luialvar/ultra_wideband_tumbler/old_uwb_reference_repo/embedded_uwb/rodos/tutorials/40-support-lib/matlib/rotations/00-referenzmanual.pdf

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

5 | Die Klasse AngleAxis
AngleAxis() | Erstellt das AngleAxis([0,0,0],0)
AngleAxis(const AngleAxis& other) | Copy-Konstruktor
AngleAxis(Vector3D& u,double phi) | Vektor-Winkel Konstruktor
AngleAxis(Quaternion& q) | Quaternion-Konstruktor
AngleAxis( Matrix3D& M) | Matrix-Konstruktor
AngleAxis(YPR& ypr) | AngleAxis Konstruktor
Quaternion toQuaternion() | AngleAxis zu Quaternion
Matrix3D toMatrix3D() | AngleAxis zu Matrix3D
YPR toYPR() | AngleAxis zu YPR
void print() | Konsolenausgabe
6 | Die Klasse Matrix4D
Matrix4D() | Erstellt die Identität
Matrix4D(Matrix3D& rot,Vector3D trans) | Matrix3D-Vector3D Konstruktor
Matrix4D(double* arr) | Array-Konstruktor
Matrix4D(const Matrix4D& other) | Copy-Konstruktor
Matrix3D getRotation() | Liefert Rotationsmatrix
Vector3D getTranslation() | Liefert Translation
Matrix4D scale(double factor) | homogene Matrixskalierung
Matrix4D mMult(const Matrix4D& right) | Matrixmultiplikation
Matrix4D invert() | inversion der Matrix4D
void print() | Konsolenausgabe
7 | Die Klasse CoordinateFrame3D
CoordinateFrame3D() | Erstellt ein Frame aus 4 Nullvektoren
CoordinateFrame3D(Vector3D& x, Vector3D& y,
Vector3D& z, Vector3D& origin) | 4 Vektor-Konstruktor
CoordinateFrame3D(Vector3D& x, Vector3D& y,
Vector3D& origin) | TRIAD-Konstruktor
CoordinateFrame3D(const CoordinateFrame3D& other) | Copy-Konstruktor
Matrix4D mapTo(CoordinateFrame3D& other) | Matrix4D von this nach other
CoordinateFrame3D translate(Vector3D& trans) | Verschiebt den Frame
CoordinateFrame3D rotate(Matrix3D& rot) | Rotiert den Frame mit einer Matrix
CoordinateFrame3D rotate(Quaternion& q) | Rotiert den Frame mit einem Quaternion
8 | Die Klasse TwoLineElement
TwoLineElement(string* twoLine) | Erstellt aus Stringarray ein TLE
9 | Die Klasse ComputationModel
ComputationModel(TwoLineElement tle) | TLE-Konstruktor
double* sgp4(double elapsedTime, TwoLineElement tle) | Berechnet Position nach SGP4

3

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
