luialvar/ultra_wideband_tumbler/old_uwb_reference_repo/embedded_uwb/rodos/tutorials/40-support-lib/matlib/rotations/00-praesentation.pdf

## Mathematische Bibliothek für Koordinatentransformationen und Rotationen

Markus Krug

2. Juli 2012
Markus Krug | Mathematische Bibliothek für Koordinatentransformationen und Rotationen

## Themen der Arbeit

Entwurf einer mathematischen Bibliothek für C++

## Themen der Arbeit

Entwurf einer mathematischen Bibliothek für C++ Quaternionen

## Themen der Arbeit

Entwurf einer mathematischen Bibliothek für C++ Quaternionen
Rotationsmatrizen

## Themen der Arbeit

Entwurf einer mathematischen Bibliothek für C++ Quaternionen
Rotationsmatrizen
homogene Koordinaten

## Themen der Arbeit

Entwurf einer mathematischen Bibliothek für C++ Quaternionen
Rotationsmatrizen
homogene Koordinaten
Koordinatentransformationen

## Themen der Arbeit

Entwurf einer mathematischen Bibliothek für C++ Quaternionen
Rotationsmatrizen
homogene Koordinaten
Koordinatentransformationen Fast-Fouriertransformation

## Themen der Arbeit

Entwurf einer mathematischen Bibliothek für C++ Quaternionen
Rotationsmatrizen
homogene Koordinaten
Koordinatentransformationen Fast-Fouriertransformation Kalmanlter

## Rotationen im R

2

0

y

x

v

φ

Vektor ~v mit φ = 45◦

## Rotationen im R

2

0

y

x

v

φ

0

Vektor ~v mit φ

0 = 60◦

## Rotationen im R

2

Was ist passiert?

## Rotationen im R

2

Was ist passiert?
eine Rotation von ~v um die z-Achse mit 15◦ (im Uhrzeigersinn)

## Rotationen im R

2

Was ist passiert?
eine Rotation von ~v um die z-Achse mit 15◦ (im Uhrzeigersinn)
eine Rotation des Koordinatensystems um −15◦ (gegen den
Uhrzeigersinn)

## Rotationen im R

2

Was ist passiert?
eine Rotation von ~v um die z-Achse mit 15◦ (im Uhrzeigersinn)
eine Rotation des Koordinatensystems um −15◦ (gegen den
Uhrzeigersinn)
eine Rotation von ~v um die z-Achse mit −345◦ (gegen den
Uhrezeigersinn)

## Rotationen im R

2

Was ist passiert?
eine Rotation von ~v um die z-Achse mit 15◦ (im Uhrzeigersinn)
eine Rotation des Koordinatensystems um −15◦ (gegen den
Uhrzeigersinn)
eine Rotation von ~v um die z-Achse mit −345◦ (gegen den
Uhrezeigersinn)
eine Rotation des Koordinatensystems um 345◦ (im
Uhrzeigersinn)

## Rotationen im R

2

Was ist passiert?
eine Rotation von ~v um die z-Achse mit 15◦ (im Uhrzeigersinn)
eine Rotation des Koordinatensystems um −15◦ (gegen den
Uhrzeigersinn)
eine Rotation von ~v um die z-Achse mit −345◦ (gegen den
Uhrezeigersinn)
eine Rotation des Koordinatensystems um 345◦
(im
Uhrzeigersinn)
⇒ es muss immer dazugesagt werden wovon man gerade Redet sonst stets Unklar !

## Möglichkeiten eine Rotation zu beschreiben

Welche Möglichkeiten gibt es eine Rotation zu beschreiben ?

## Möglichkeiten eine Rotation zu beschreiben

Welche Möglichkeiten gibt es eine Rotation zu beschreiben ? 1 Rotationsmatrizen

## Möglichkeiten eine Rotation zu beschreiben

Welche Möglichkeiten gibt es eine Rotation zu beschreiben ?
1 | Rotationsmatrizen
2 | Achse und Winkel

## Möglichkeiten eine Rotation zu beschreiben

Welche Möglichkeiten gibt es eine Rotation zu beschreiben ?
1 | Rotationsmatrizen
2 | Achse und Winkel
3 | Eulerwinkel(in der Luftfahrt Yaw,Pitch und Roll)

## Möglichkeiten eine Rotation zu beschreiben

Welche Möglichkeiten gibt es eine Rotation zu beschreiben ?
1 | Rotationsmatrizen
2 | Achse und Winkel
3 | Eulerwinkel(in der Luftfahrt Yaw,Pitch und Roll)
4 | Quaternionen

## Beschreibung durch eine Rotationsmatrix

Zurück zum Beispiel: 0

y

x

v

φ
x1

y1

x1 = cos φ · |~v|
y1 = sin φ · |~v|

## Beschreibung durch eine Rotationsmatrix

Analog gilt: 0

y

x

v

φ

0
x2

y2

x2 = cos φ

0
- |~v|
y2 = sin φ

0
- |~v|

## Additionstheoreme, jeder kennt sie keiner kann sie

mit φ

0 = φ + α folgt:

x2 =

cos φ cos α−sin φ sin α
z | }| | {
cos(φ + α) | ·|~v|
y2 = | sin(φ + α)
| | {z | }
sin φ cos α+sin α cos φ

·|~v|

x2 = cos φ · |~v|
| {z | }
x1 | | cos α − sin φ · |~v|
| {z | }
y1

cos α

y2 = sin φ · |~v|
| {z }
y1

cos α + cos φ · |~v|
| {z }
x1

sin α

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

## Ausdehnung auf den R

3

Da die Rotation ausschlieÿlich in der xy-Ebene stattndet, so wird die z-Komponente des Vektors ~v nicht verändert
⇒ es wurde die Fundamentalmatrix um die z-Achse gefunden:

Rz (α) =

cos α − sin α 0
sin α | cos α | 0
0 | 0 | 1

## Fundamentalrotationen

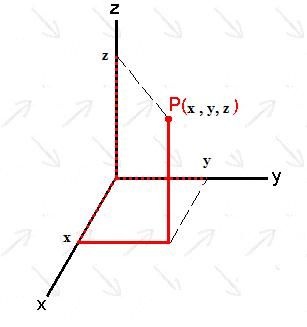
[picture p46: figure]

Abbildung : Die Projektion in die xy-Ebene

## Fundamentalrotationen

Betrachtet man nun Projektionen in die xz bzw. yz-Ebene, so erhält man die Fundamentalrotationsmatrizen:

Rz (α) =

cos α − sin α 0
sin α | cos α | 0
0 | 0 | 1

Ry (β) =

cos β | 0 sin β
0 | 1 | 0
− sin β 0 cos β

Rx (γ) =

1 | 0 | 0
0 cos γ − sin γ
0 sin γ cos γ

## Fundamentalrotationen

# Was bringt uns das nun ?

## Fundamentalrotationen

Was bringt uns das nun ?

W
ir können mit Hilfe einer einfachen Rechenvorschrift eine Rotation eines Vektors ~v mit einen Winkel φ um eine der Koordinatenachsen vollziehen

w~ = R(φ) · ~v

## Fundamentalrotationen

# Was können wir noch nicht ?

## Fundamentalrotationen

Was können wir noch nicht ?
⇒ eine Rotation um einen beliebigen Vektor

## Fundamentalrotationen

Was können wir noch nicht ?
⇒ eine Rotation um einen beliebigen Vektor Abhilfe schat das Theorem von Euler:

Satz (Eulers Theorem)
Zwei voneinander unabhängige, orthonormale Koordinatensysteme können durch eine Folge von nicht mehr als 3 Fundamentalrotationen, wobei keine zwei aufeinanderfolgenden Rotationen um die selbe Achse erfolgen, ineinander überführt werden.

## Eulerwinkel

Es ergeben sich folgende 12 Möglichkeiten das Eulertheorem anzuwenden:
xyz yzx zxy
xzy yxz zyx
xyx yzy zxz
xzx yxy zyz

## Eulerwinkel

Es ergeben sich folgende 12 Möglichkeiten das Eulertheorem anzuwenden:
xyz yzx zxy
xzy yxz zyx
xyx yzy zxz
xzx yxy zyz
zyx bedeutet beispielsweise:

1 eine Rotation um die z-Achse

## Eulerwinkel

Es ergeben sich folgende 12 Möglichkeiten das Eulertheorem anzuwenden:
xyz yzx zxy
xzy yxz zyx
xyx yzy zxz
xzx yxy zyz
zyx bedeutet beispielsweise:
1 | eine Rotation um die z-Achse
2 | eine Rotation um die neue y-Achse

## Eulerwinkel

Es ergeben sich folgende 12 Möglichkeiten das Eulertheorem anzuwenden:
xyz yzx zxy
xzy yxz zyx
xyx yzy zxz
xzx yxy zyz
zyx bedeutet beispielsweise:
1 | eine Rotation um die z-Achse
2 | eine Rotation um die neue y-Achse
3 | eine Rotation um die neue x-Achse

## Eulerwinkel

Es ergeben sich folgende 12 Möglichkeiten das Eulertheorem anzuwenden:
xyz yzx zxy
xzy yxz zyx
xyx yzy zxz
xzx yxy zyz
zyx bedeutet beispielsweise:
1 | eine Rotation um die z-Achse
2 | eine Rotation um die neue y-Achse
3 | eine Rotation um die neue x-Achse

⇒ Yaw-Pitch-Roll Luftfahrtsequenz

## Rotationssequenzen

Das Schlüsselwort neue:
Es ergeben sich 2 Möglichkeiten die Eulersequenz nachzurechnen:

Multiplikation von rechts

## Rotationssequenzen

Das Schlüsselwort neue:
Es ergeben sich 2 Möglichkeiten die Eulersequenz nachzurechnen:

Multiplikation von rechts
Multiplikation von links

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

## Rotationssequenzen

Goldene Merkregel für Rotationssequenzen:

Faustregel (Rotationssequenzen)
Erfolgt eine Rotation um eine der xen Achsen, so ist stets von links zu Multiplizieren, eine Rotation um eine der neuen Achsen wird stets von rechts Multipliziert.

## Eulerwinkel

Für die zuvor vorgestellte Eulersequenz zyx gilt also:

Rzyx (α, β, γ) = Rz (α) · Ry (β) · Rx (γ)

Die Winkel α, β, γ werden als Eulerwinkel bezeichnet

## Yaw-Pitch-Roll Matrix

Für die zuvor vorgestellte Eulersequenz zyx gilt also:

Rzyx (α, β, γ) = Rz (α) · Ry (β) · Rx (γ)

=

cos α cos β cos α sin β sin γ − sin α cos γ cos α sin β cos γ + sin α sin γ
sin α cos β | sin α sin β sin γ + cos α cos γ sin α sin β cos γ − cos α sin γ
− sin β | cos β sin γ | cos β cos γ

!

## YPR Matrix

Was haben wir gelernt:
Mit Hilfe der YPR-Matrix können wir also einen Vektor mit den Eulerwinkeln drehen.

## YPR Matrix

Was haben wir gelernt:
Mit Hilfe der YPR-Matrix können wir also einen Vektor mit den Eulerwinkeln drehen.
Wir sind nicht mehr eingeschränkt auf reine Rotationen um die Koordinatensystemachsen.

## YPR Matrix

Was haben wir gelernt:
Mit Hilfe der YPR-Matrix können wir also einen Vektor mit den Eulerwinkeln drehen.
Wir sind nicht mehr eingeschränkt auf reine Rotationen um die Koordinatensystemachsen.
Was wir jedoch immer noch nicht können ist eine Rotation um einen beliebigen Vektor und Winkel

## allgemeine Rotationsmatrix

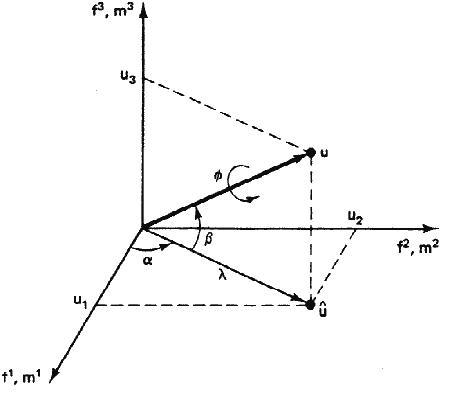
[picture p47: figure]

Abbildung : Eine Rotation um einen beliebigen Vektor ~u mit Winkel φ

## allgemeine Rotationsmatrix

Zur Herleitung der allgemeinen Matrix müssen folgende Schritte ausgeführt werden:

## allgemeine Rotationsmatrix

Zur Herleitung der allgemeinen Matrix müssen folgende Schritte ausgeführt werden:
1 Drehe M um m³ mit dem Winkel α

## allgemeine Rotationsmatrix

Zur Herleitung der allgemeinen Matrix müssen folgende Schritte ausgeführt werden:
1 | Drehe M um m³ mit dem Winkel α
2 | Drehe M um m² mit dem Winkel −β

## allgemeine Rotationsmatrix

Zur Herleitung der allgemeinen Matrix müssen folgende Schritte ausgeführt werden:
1 | Drehe M um m³ mit dem Winkel α
2 | Drehe M um m² mit dem Winkel −β
3 | Drehe M um m¹ mit dem Winkel φ

## allgemeine Rotationsmatrix

Zur Herleitung der allgemeinen Matrix müssen folgende Schritte ausgeführt werden:
1 | Drehe M um m³ mit dem Winkel α
2 | Drehe M um m² mit dem Winkel −β
3 | Drehe M um m¹ mit dem Winkel φ
4 | Drehe M um m² mit dem Winkel β

## allgemeine Rotationsmatrix

Zur Herleitung der allgemeinen Matrix müssen folgende Schritte ausgeführt werden:
1 | Drehe M um m³ mit dem Winkel α
2 | Drehe M um m² mit dem Winkel −β
3 | Drehe M um m¹ mit dem Winkel φ
4 | Drehe M um m² mit dem Winkel β
5 | Drehe M um m³ mit dem Winkel −α

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

## kleine Ergebniszusammenfassung

Wir können nun:
Rotationen um die Koordinatenachsen
Rotationen mit Hilfe von Eulerwinkeln
Rotationen um einen beliebigen Vektor mit einem beliebigen Winkel

## kleine Ergebniszusammenfassung

Wir können nun:
Rotationen um die Koordinatenachsen
Rotationen mit Hilfe von Eulerwinkeln
Rotationen um einen beliebigen Vektor mit einem beliebigen Winkel
Doch alles hat noch einen Nachteil:
⇒ wir müssen stets zuerst die Rotationsmatrix bilden und damit die Rotation ausführen

w~ = R · ~v

## Rodrigues Rotationsformel

Betrachtet man die allgemeine Rotation eines Vektors ~v =

v1
v2
v3

mit der allgemeinen Rotationsmatrix:

w~ =

u

2

x

(1 − cos φ) + cos φ | ux uy (1 − cos φ) − uz sin φ | ux uz (1 − cos φ) + uy sin φ
ux uy (1 − cos φ) + uz sin φ | u
| 2 y
| (1 − cos φ) + cos φ | uy uz (1 − cos φ) − ux sin φ
ux uz (1 − cos φ) − uy sin φ | uy uz (1 − cos φ) + ux sin φ | u
| | 2 z (1 − cos φ) + cos φ
- ~v

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

## Rodrigues Rotationsformel

Cleveres zusammenfassen ergibt die Rodrigues Rotationsformel:

vRot ~ = ~v cos φ + (~u × ~v)sin φ + ~u(~u · ~v)(1 − cos φ)

## Rodrigues Rotationsformel

Cleveres zusammenfassen ergibt die Rodrigues Rotationsformel:

vRot ~ = ~v cos φ + (~u × ~v)sin φ + ~u(~u · ~v)(1 − cos φ)

⇒ es ist also auch möglich einen Vektor um einen gegebenen Vektor (und Winkel) zu rotieren ohne zunächst die allgemeine Rotationsmatrix bilden zu müssen.

## Vor- und Nachteile der bisherigen Darstellungen

Vorteile der Eulerwinkel:
nur 3 Variablen müssen gespeichert werden
am einfachsten aus den Sensordaten zu gewinnen (Strapdown-Algorithmus)

## Vor- und Nachteile der bisherigen Darstellungen

Nachteile der Eulerwinkel:
es muss jedesmal zunächst die Rotationsmatrix gebildet werden Gimbal Locks

## Vor- und Nachteile der bisherigen Darstellungen

Vorteile der Achse-Winkel Darstellung
es kann ohne die Rotationsmatrix bilden zu müssen rotiert werden
Skaliert man den Winkel in die Länge des Vektors nur 3 Variablen zu speichern

## Vor- und Nachteile der bisherigen Darstellungen

Nachteile der Achse-Winkel Darstellung
es können keine Rotationssequenzen berechnet werden (immer einzeln !)

## Vor- und Nachteile der bisherigen Darstellungen

Vorteile der Rotationsmatrizen allgemein relativ anschaulich

## Vor- und Nachteile der bisherigen Darstellungen

Nachteile der Rotationsmatrizen sehr Rechenaufwändig
sehr Speicheraufwändig

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

## Quaternionen

Quaternionen H als Hyperkomplexe Zahlen des Ranges 4

Angefangen bei R

Verdopplungssatz
z}|{ ⇒ | C

von den komplexen Zahlen C

Verdopplungssatz
z}|{ ⇒ | H

Quaternion ist also ein 4-Tupel
(q0, q1, q2, q3) = q0 + iq1 + jq2 + kq3

## Quaternionen

i, j, k interpretiert man als Einheitsvektoren im 3-dimensionalen Raum.
Die Quaternionen enthalten also den R

3
als Spezialfall für q0 = 0 Ein 3-dimensionaler Vektor ~v kann mit Hilfe der Quaternionen also dargestellt werden,als:

~v = 0 + ~v = q0 + ~q

## Quaternionen-Rechenregeln

Analog zum R

4 deniert man die Gleichheit zweier Quaternionen p und q, als:
q0 = p0 | q1 = p1 | q2 = p2 | q3 = p3

## Quaternionen-Rechenregeln

Analog zum R

4 deniert man die Gleichheit zweier Quaternionen p und q, als:
q0 = p0 | q1 = p1 | q2 = p2 | q3 = p3
und deren Addition:

p + q = (p0 + q0) + i(p1 + q1) + j(p2 + q2) + k(p3 + q3)

## Quaternionen-Multiplikation

Multipliziert man nach altbekannten Rechenregeln zwei Quaternion p und q, so erhält man :

pq = (p0 + p1 + p2 + p3)(q0 + q1 + q2 + q3)

## Quaternionen-Multiplikation

Multipliziert man nach altbekannten Rechenregeln zwei Quaternion p und q, so erhält man :

pq = (p0 + p1 + p2 + p3)(q0 + q1 + q2 + q3) = p0q0 + ip0q1 + jp0q2 + kp0q3

+ ip1q0 + i

2
p1q1 + ijp1q2 + ikp1q3

+ jp2q0 + jip2q1 + j

2
p2q2 + jkp2q3

+ kp3q0 + kip3q1 + kjp3q2 + k

2
p3q3

## Quaternionen-Multiplikation

Um daraus ein nützliches Ergebnis ziehen zu können benötigen wir die Rechenregeln von Hamilton

i

2 = j

2 = k

2 = ijk = −1

ij = k = −ji
jk = i = −kj
ki = j = −ik

## Quaternionen-Multiplikation

Um daraus ein nützliches Ergebnis ziehen zu können benötigen wir die Rechenregeln von Hamilton

i

2 = j

2 = k

2 = ijk = −1

ij = k = −ji
jk = i = −kj
ki = j = −ik

mit deren Hilfe dann gilt:

pq = p0q0 − (p1q1 + p2q2 + p3q3)
+ p0(iq1 + jq2 + kq3) + q0(ip1 + jp2 + kp3)
+ i(p2q3 − p3q2) + j(p3q1 − p1q3) + k(p1q2 − p2q1)

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

## Quaternionen-Multiplikation

pq = p0q0 −

~p·~q
z | }| | {
(p1q1 + p2q2 + p3q3)

+

p0·~q
z | }| | {
p0(iq1 + jq2 + kq3) +q0(ip1 + jp2 + kp3)
+ i(p2q3 − p3q2) + j(p3q1 − p1q3) + k(p1q2 − p2q1)

## Quaternionen-Multiplikation

pq = p0q0 −

~p·~q
z | }| | {
(p1q1 + p2q2 + p3q3)

+

p0·~q
z | }| | {
p0(iq1 + jq2 + kq3) +

q0·~p
z | }| | {
q0(ip1 + jp2 + kp3)
+ i(p2q3 − p3q2) + j(p3q1 − p1q3) + k(p1q2 − p2q1)

## Quaternionen-Multiplikation

pq = p0q0 −

~p·~q
z | }| | {
(p1q1 + p2q2 + p3q3)

+

p0·~q
z | }| | {
p0(iq1 + jq2 + kq3) +

q0·~p
z | }| | {
q0(ip1 + jp2 + kp3)
+ i(p2q3 − p3q2) + j(p3q1 − p1q3) + k(p1q2 − p2q1)
| | {z | }
~p×~q

## Quaternionen-Multiplikation

Damit wurde die wohl am leichtesten per Hand zu berechnende Variante gefunden:

pq = p0q0 − ~p · ~q + p0~q + q0~p + ~p × ~q

oder analog in Matrixschreibweise:

pq = r =

r0
r1
r2
r3

=

p0 | −p1 | −p2 | −p3
p1 | p0 | −p3 | p2
p2 | p3 | p0 | −p1
p3 | −p2 | p1 | p0

q0
q1
q2
q3

## konjugiertes Quaternionen

Zum Beschreiben, warum ein Quaternion eine Rotation darstellt, wird noch eine letzte Rechenregel für Quaternionen benötigt, ähnlich wie bei den komplexen Zahlen C deniert man sich das konjugierte Quaternion als:

q

∗ = q0 − (iq1 + jq2 + kq3)

## Das Quaternion als Rotation

Zurück zu Rotationsmatrizen, wir wissen:

w~ = R · ~v

beschreibt eine Rotation mit einer Matrix. Gesucht ist nun ein ähnlicher Audruck für ein Quaternion.

## Das Quaternion als Rotation

Zurück zu Rotationsmatrizen, wir wissen:

w~ = R · ~v

beschreibt eine Rotation mit einer Matrix. Gesucht ist nun ein ähnlicher Audruck für ein Quaternion. Instinktiv versucht man zunächst:

w~ = q · ~v

Berechnet man nun das obige Quaternionenprodukt, so ergibt sich:

w~ = q · ~v = (q0 + ~q)(0 + ~v)
= q0 · 0 − ~q · ~v + 0 · ~q + q0~v + ~q × ~v = −~q · ~v + q0~v + ~q × ~v

## Das Quaternion als Rotation

Zurück zu Rotationsmatrizen, wir wissen:

w~ = R · ~v

beschreibt eine Rotation mit einer Matrix. Gesucht ist nun ein ähnlicher Audruck für ein Quaternion. Instinktiv versucht man zunächst:

w~ = q · ~v

Berechnet man nun das obige Quaternionenprodukt, so ergibt sich:

w~ = q · ~v = (q0 + ~q)(0 + ~v)
= q0 · 0 − ~q · ~v + 0 · ~q + q0~v + ~q × ~v = −~q · ~v + q0~v + ~q × ~v

Wir liegen nur in R

3
, wenn q0 = 0 und damit:

~q · ~v = 0

## Das Quaternion als Rotation

Wir liegen also nur in R

3
, wenn ~q senkrecht auf ~v steht: ⇒erster Ansatz im allgemeinen nicht aufrecht zu erhalten ! Zweiter Ansatz:
vpq , vqp , pqv
qpv , pvq , qvp

## Das Quaternion als Rotation

Wir liegen also nur in R

3
, wenn ~q senkrecht auf ~v steht: ⇒erster Ansatz im allgemeinen nicht aufrecht zu erhalten ! Zweiter Ansatz:
vpq , vqp , pqv
qpv , pvq , qvp
Das Produkt pq ist wieder ein Quaternion also bleibt nur pvq und qvp.

## Das Quaternion als Rotation

Berechnet man das Produkt p~v q, so ergibt sich für den skalaren Anteil w0:

w0 = −q0(~p · ~v) − p0(~v · ~q) + (~p × ~q) · ~v

## Das Quaternion als Rotation

Berechnet man das Produkt p~v q, so ergibt sich für den skalaren Anteil w0:

w0 = −q0(~p · ~v) − p0(~v · ~q) + (~p × ~q) · ~v

Setzt man nun noch q = p

∗
ein, so folgt:

w0 = −p0(~p · ~v) − p0(~v · −~p) + (~p × −~p) · ~v = −p0[~p · ~v + (−~v · ~p)] + 0

= 0

## Das Quaternion als Rotation

Berechnet man das Produkt p~v q, so ergibt sich für den skalaren Anteil w0:

w0 = −q0(~p · ~v) − p0(~v · ~q) + (~p × ~q) · ~v

Setzt man nun noch q = p

∗
ein, so folgt:

w0 = −p0(~p · ~v) − p0(~v · −~p) + (~p × −~p) · ~v = −p0[~p · ~v + (−~v · ~p)] + 0

= 0

Ab jetzt wird der Term q~v q∗ als Quaternionenrotationsoperator Lv (q) bezeichnet.

## Quaternionen-Der Achse-Winkel Charakter

Wir wissen q = q0 + ~q.
Für ein normiertes Quaternion gilt:

q

2
0 + |~q|

2 = 1

## Quaternionen-Der Achse-Winkel Charakter

Wir wissen q = q0 + ~q.
Für ein normiertes Quaternion gilt:

q

2
0 + |~q|

2 = 1

Erinnerung: Pythagoras am Einheitskreis!

cos² φ + sin² φ = 1

## Quaternionen-Der Achse-Winkel Charakter

Wir wissen q = q0 + ~q.
Für ein normiertes Quaternion gilt:

q

2
0 + |~q|

2 = 1

Erinnerung: Pythagoras am Einheitskreis!

cos² φ + sin² φ = 1

Daraus folgern wir:

cos² φ = q

2
0
sin² φ = |~q|

2

## Quaternionen-Der Achse-Winkel Charakter

Wir wissen q = q0 + ~q.
Für ein normiertes Quaternion gilt:

q

2
0 + |~q|

2 = 1

Erinnerung: Pythagoras am Einheitskreis!

cos² φ + sin² φ = 1

Daraus folgern wir:

cos² φ = q

2
0
sin² φ = |~q|

2

Man kann also allgemein für ein Quaternion schreiben:

q = q0 + ~q = cos φ + ~u sin φ

## Quaternionen-Der Achse-Winkel Charakter

q = q0 + ~q = cos φ + ~u sin φ

## Quaternionen-Der Achse-Winkel Charakter

q = q0 + ~q = cos φ + ~u sin φ

~u wird sich noch als Rotationsachse herausstellen

## Quaternionen-Der Achse-Winkel Charakter

q = q0 + ~q = cos φ + ~u sin φ

~u wird sich noch als Rotationsachse herausstellen φ scheint in jedem Fall im Zusammenhang mit dem Rotationswinkel zu stehen

## Quaternionen-Der Achse-Winkel Charakter

q = q0 + ~q = cos φ + ~u sin φ

~u wird sich noch als Rotationsachse herausstellen
φ scheint in jedem Fall im Zusammenhang mit dem Rotationswinkel zu stehen
⇒ der Achse-Winkel Charackter des Quaternions wird deutlich!

## Quaternionen-Der Achse-Winkel Charakter

q = q0 + ~q = cos φ + ~u sin φ

~u wird sich noch als Rotationsachse herausstellen
φ scheint in jedem Fall im Zusammenhang mit dem Rotationswinkel zu stehen
⇒ der Achse-Winkel Charackter des Quaternions wird deutlich! es wird nun Zeit zu zeigen, dass das Quaternion auch eine Rotation darstellt!

## Quaternionen-Der Achse-Winkel Charakter

q = q0 + ~q = cos φ + ~u sin φ

~u wird sich noch als Rotationsachse herausstellen
φ scheint in jedem Fall im Zusammenhang mit dem Rotationswinkel zu stehen
⇒ der Achse-Winkel Charackter des Quaternions wird deutlich! es wird nun Zeit zu zeigen, dass das Quaternion auch eine Rotation darstellt!
Ab jetzt im Hinterkopf behalten, wir behandeln normierte Quaternionen

## Der Quaternionrotationsoperator Lq(v)

Wir benötigen noch eine Kurzschreibweise:

Lq(v) = q~v q∗

Und das fertig vereinfachte Ergebnis der Multiplikation:

w~ = qvq∗ = (q0 + ~q)(0 + ~v)(q0 − ~q)

## Der Quaternionrotationsoperator Lq(v)

Wir benötigen noch eine Kurzschreibweise:

Lq(v) = q~v q∗

Und das fertig vereinfachte Ergebnis der Multiplikation:

w~ = qvq∗ = (q0 + ~q)(0 + ~v)(q0 − ~q)

= (2q

2
0 − 1)~v + 2(~q · ~v)~q + 2q0(~q × ~v)

## Der Quaternionrotationsoperator Lq(v)

Wir benötigen noch eine Kurzschreibweise:

Lq(v) = q~v q∗

Und das fertig vereinfachte Ergebnis der Multiplikation:

w~ = qvq∗ = (q0 + ~q)(0 + ~v)(q0 − ~q)

= (2q

2
0 − 1)~v + 2(~q · ~v)~q + 2q0(~q × ~v)

= (q

2
0 − |~q|

2
)~v + 2(~q · ~v)~q + 2q0(~q × ~v)

## Der Quaternionrotationsoperator Lq(v)

Wir benötigen noch eine Kurzschreibweise:

Lq(v) = q~v q∗

Und das fertig vereinfachte Ergebnis der Multiplikation:

w~ = qvq∗ = (q0 + ~q)(0 + ~v)(q0 − ~q)

= (2q

2
0 − 1)~v + 2(~q · ~v)~q + 2q0(~q × ~v)

= (q

2
0 − |~q|

2
)~v + 2(~q · ~v)~q + 2q0(~q × ~v)

Sowie 2 Eigenschaften des Operators:
1 | Linearität I : Lq(a + b) = Lq(a) + Lq(b)
2 | Linearität II: Lq(ka) = k · Lq(a)

## Beweis- Lq(v) beschreibt eine Rotation

Trick: zerlege den zu rotierenden Vektor ~v in 2 Teile:

~v =

parallel zu ~q
z}|{
~a +

senkrecht zu ~q
z}|{
~n = k~q + ~n
w~ = ~b + m~

## Beweis- Lq(v) beschreibt eine Rotation

Trick: zerlege den zu rotierenden Vektor ~v in 2 Teile:

~v =

parallel zu ~q
z}|{
~a +

senkrecht zu ~q
z}|{
~n = k~q + ~n
w~ = ~b + m~

Was uns schon klar sein sollte, der zur Rotationsachse parallel Anteil bleibt bei der Rotation unverändert!

## Der parallele Anteil a

Wegen der Linearität von Lq(v) gilt:

w~ = Lq(v) = Lq(a + n) = Lq(a) + Lq(n)

Was uns erlaubt beide Teile separat zu betrachten.

## Der parallele Anteil a

Wegen der Linearität von Lq(v) gilt:

w~ = Lq(v) = Lq(a + n) = Lq(a) + Lq(n)

Was uns erlaubt beide Teile separat zu betrachten.

Lq(a) = Lq(k · ~q) Wobei k ein Skalar darstellt = q(k~q)q

∗

= (q

2
0 − |~q|

2
)(k~q) + 2(~q · k~q)~q + 2q0(~q × k~q) = kq²
0

~q − k|~q|

2
~q + 2k|~q|

2
~q

= k(q

2
0 + |~q|

2
)
= k~q = a

## Der senkrechte Anteil

Lq(n) = (q

2
0 − |~q|

2
)n + 2q0|~q|(~u × ~n)
= n(cos² φ − sin² φ) + 2 cos φ sin φ(~u × ~n)

= n cos(2φ) + (~u × ~n)sin(2φ)

Vermutung: Rotation um die Achse ~u mit dem Winkel 2φ

## Vermutung bestätigen!

Lq(n) = n cos(2φ) + (~u × ~n)sin(2φ)

Wir haben bereits gelernt wie man einen Vektor ~v um einen gegebenen Vektor und einen gegebenen Winkel rotiert.

## Vermutung bestätigen!

Lq(n) = n cos(2φ) + (~u × ~n)sin(2φ)

Wir haben bereits gelernt wie man einen Vektor ~v um einen gegebenen Vektor und einen gegebenen Winkel rotiert. ⇒ Rodrigues Rotationsformel.

## Vermutung bestätigen!

Lq(n) = n cos(2φ) + (~u × ~n)sin(2φ)

Wir haben bereits gelernt wie man einen Vektor ~v um einen gegebenen Vektor und einen gegebenen Winkel rotiert. ⇒ Rodrigues Rotationsformel.

nRot = n cos(2φ) + (~u × ~n)sin(2φ) + ~u(~u · ~n)(1 − cos(2φ) = n · cos(2φ) + (~u × ~n)sin(2φ)

## Wichtige Schlussfolgerung

Für jedes Einheitsquaternion q = q0 + ~q = cosφ + ~u sin φ und für jeden Vektor ~v ∈ R

3
, beschreibt der Quaternionrotationsoperator Lq(v) = q~v q∗
eine Rotation von ~v um die Achse ~u =

~q
|~q| mit dem
Winkel 2φ.

## Wichtige Schlussfolgerung

Für jedes Einheitsquaternion q = q0 + ~q = cosφ + ~u sin φ und für jeden Vektor ~v ∈ R

3
, beschreibt der Quaternionrotationsoperator Lq(v) = q~v q∗
eine Rotation von ~v um die Achse ~u =

~q
|~q| mit dem
Winkel 2φ.

Analog soll im Folgenden der Operator Lq
∗ = q

∗~v q deniert sein
als:

Für jedes Einheitsquaternion q = q0 + ~q = cosφ + ~u sin φ und für jeden Vektor ~v ∈ R

3
, beschreibt der Quaternionrotationsoperator Lq

∗ = q

∗~v q eine Rotation von ~v um die Achse ~u =

~q
|~q| mit dem
Winkel −2φ.

## Arten der Rotation

Es wurde nun festgestellt, dass eine Rotation über die Folgenden 2 Gleichungen ausgeführt werden kann:

w~ = R · ~v
w~ = q~v q∗

## Arten der Rotation

Es wurde nun festgestellt, dass eine Rotation über die Folgenden 2 Gleichungen ausgeführt werden kann:

w~ = R · ~v
w~ = q~v q∗

Damit kann der Zusammenhang zwischen Quaternion und Rotationsmatrix ermittelt werden:

R · ~v = q~v q∗

## Zusammenhang zwischen Quaternionen und Rotationsmatrix

es ist bereits bekannt, dass:

w~ = qvq∗

= (2q

2
0 − 1)~v + 2(~q · ~v)~q + 2q0(~q × ~v)

Betrachten wir davon nun jeden Summanden einzeln, so erhalten wir:

(2q

2
0 − 1)~v =

(2q

2
0 − 1) | 0 | 0
0 | (2q
| 2
| 0 − 1) | 0
0 | 0 | (2q
| | 2
| | 0 − 1)

v1
v2
v3

2(~v · ~q)~q =

2q

2
1
| 2q1q2 | 2q1q3
2q1q2 | 2q
| 2
| 2 | 2q2q3
2q1q3 | 2q2q3 | 2q

2
| | 3

v1
v2
v3

2q0(~q × ~v) =

0 | −2q0q3 | 2q0q2
2q0q3 | 0 | −2q0q1
−2q0q2 | 2q0q1 | 0

v1
v2
v3

## Der Zusammenhang zwischen Quaternionen und Rotationsmatrix

w1
w2
w3

!
=

2q

2
0 − 1 + 2q

2
1
| 2q1q2 − 2q0q3 | 2q1q3 + 2q0q2
2q1q2 + 2q0q3 | 2q
| 2 0 − 1 + 2q
| 2
| 2 | 2q2q3 − 2q0q1
2q1q3 − 2q0q2 | 2q2q3 + 2q0q1 | 2q

2
| | 0 − 1 + 2q

2/3! v1
v2
v3

!

w~ = qvq∗ = Qv

## Der Zusammenhang zwischen Quaternionen und Rotationsmatrix

Haben wir nun eine Matrix der Form
m11 | m12 | m13
m21 | m22 | m23
m31 | m32 | m33

Können wir beide Matrizen Gleichsetzen und erhalten 9 Gleichungen, aus denen wir Die Quaternionenelemente ermitteln:

m11 | m12 | m13
m21 | m22 | m23
m31 | m32 | m33 |
=
2q

2
0 − 1 + 2q

2
1
2q1q2 − 2q0q3 | 2q1q3 + 2q0q2
2q1q2 + 2q0q3 | 2q

2
0 − 1 + 2q

2
2

2q2q3 − 2q0q1

2q1q3 − 2q0q2 | 2q2q3 + 2q0q1 | 2q

2
0 − 1 + 2q

2
3

## Der Zusammenhang zwischen Quaternionen und Rotationsmatrix

m11 | m12 | m13
m21 | m22 | m23
m31 | m32 | m33 |
=
2q

2
0 − 1 + 2q

2
1
2q1q2 − 2q0q3 | 2q1q3 + 2q0q2
2q1q2 + 2q0q3 | 2q

2
0 − 1 + 2q

2
2

2q2q3 − 2q0q1

2q1q3 − 2q0q2 | 2q2q3 + 2q0q1 | 2q

2
0 − 1 + 2q

2
3

# Ideen?

## erster Ansatz

berechne die Spur der Matrix Q

Spur(Q) = 4q

2
0 − 3 + 2(q

2
0 + q

2
1 + q

2
2 + q

2/3) = 4q

2
0 − 1

q0 =

1
2

√
m11 + m22 + m33 + 1

## erster Ansatz

berechne die Spur der Matrix Q

Spur(Q) = 4q

2
0 − 3 + 2(q

2
0 + q

2
1 + q

2
2 + q

2/3) = 4q

2
0 − 1

q0 =

1
2

√
m11 + m22 + m33 + 1

Die anderen Komponenten lassen sich mit Hilfe von q0 schnell ermitteln:

4q0q1 = m32 − m23

4q0q2 = m13 − m31

4q0q3 = m21 − m12

## erster Ansatz

berechne die Spur der Matrix Q

Spur(Q) = 4q

2
0 − 3 + 2(q

2
0 + q

2
1 + q

2
2 + q

2/3) = 4q

2
0 − 1

q0 =

1
2

√
m11 + m22 + m33 + 1

Die anderen Komponenten lassen sich mit Hilfe von q0 schnell ermitteln:

4q0q1 = m32 − m23

4q0q2 = m13 − m31

4q0q3 = m21 − m12

Was könnte hier schief laufen ?

## Der Zusammenhang zwischen Quaternionen und Rotationsmatrix

solange q0 reell oder 6= 0 gibt es keine Probleme
Die Richtung Quaternion → Rotationsmatrix ist leicht

Doch unsere Lösungsstrategie versagt, falls einer der obigen Fälle eintritt.
Abhilfe schat ein Verfahren, dass diese Fälle gesondert betrachtet.

## Der Algorithmus zum Umwandeln Rotationsmatrix <-> Quaternion

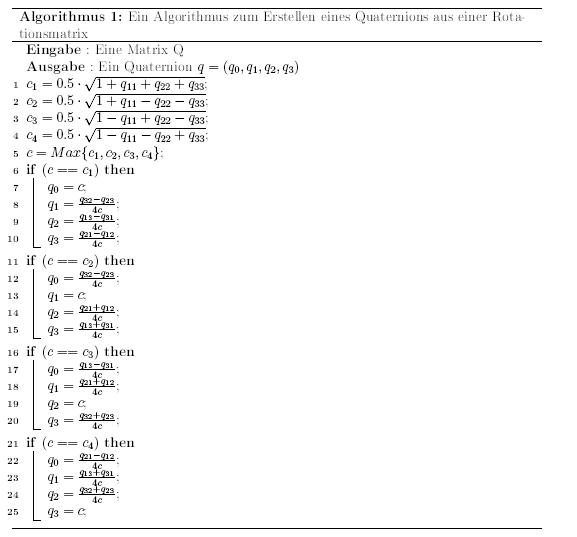
[picture p48: figure]

## Der Zusammenhang zwischen Quaternion und Eulerwinkeln

durch einen ähnlichen Vergleich lässt sich der Zusammenhang zwischen Eulerwinkeln und Quaternionen errechnen Betrachte zunächst die YPR Sequenz mit Hilfe von Quaternionen

YPR-Sequenz
Die YPR Sequenz stellt eine Rotation um die z-Achse mit dem Winkel α, gefolgt von einer Rotation um die neue y-Achse mit Winkel β und anschlieÿend eine Rotation um die neue x-Achse mit Winkel γ dar.

## Der Zusammenhang zwischen Quaternion und Eulerwinkeln

Oder etwas mathematischer

qypr = qzqyqx

## Der Zusammenhang zwischen Quaternion und Eulerwinkeln

Oder etwas mathematischer

qypr = qzqyqx

wobei zunächst eine Rotation um die z-Achse(k) mit α:

qz = cos(

α
2

) + k sin(

α
2

)

## Der Zusammenhang zwischen Quaternion und Eulerwinkeln

Oder etwas mathematischer

qypr = qzqyqx

wobei zunächst eine Rotation um die z-Achse(k) mit α:

qz = cos(

α
2

) + k sin(

α
2

)

anschlieÿend eine Rotation um die y-Achse(j) mit β (Pitch):

qy = cos(

β
2

) + j sin(

β
2

)

## Der Zusammenhang zwischen Quaternion und Eulerwinkeln

Oder etwas mathematischer

qypr = qzqyqx

wobei zunächst eine Rotation um die z-Achse(k) mit α:

qz = cos(

α
2

) + k sin(

α
2

)

anschlieÿend eine Rotation um die y-Achse(j) mit β (Pitch):

qy = cos(

β
2

) + j sin(

β
2

)

und letztendlich eine Rotation um die x-Achse(i) mit γ(Roll):

qx = cos(

γ
2

) + i sin(

γ
2

)

## Der Zusammenhang zwischen Quaternion und Eulerwinkeln

qypr = qzqyqx = q0 + iq1 + jq2 + kq3 wobei

q0 = cos(

α
2

) cos(

β
2

) cos(

γ
2

) + sin(

α

2 | )sin( β
| 2 )sin(

γ
2

)

q1 = cos(

α
2

) cos(

β
2

)sin(

γ
2

) − sin(

α
2

)sin(

| β
| 2 ) cos(

γ
2

)

q2 = cos(

α
2

)sin(

β
2

) cos(

γ
2

) + sin(

α
2

) cos(

| β
| 2 )sin(

γ
2

)

q3 = sin(

α
2

) cos(

β
2

) cos(

γ
2

) − cos(

α

2 | )sin( β
| 2 )sin(

γ
2

)

## Zwischenstand

Was fehlt noch ?

Bestimmung der Eulerwinkel aus einer beliebigen Rotationsmatrix
Bestimmung von Achse und Winkel aus einer beliebigen Rotationsmatrix
Bestimmung der Eulerwinkel aus einem Quaternion Bestimmung der Achse und Winkel aus einem Quaternion Bestimmung von Achse und Winkel aus den Eulerwinkeln Bestimmung der Eulerwinkel aus Achse und Winkel

## Vergleich der Ezienz

Vergleich von Quaternionen, Rotationsmatrizen , Achse-Winkel und Eulerwinkel Darstellung in:

## Vergleich der Ezienz

Vergleich von Quaternionen, Rotationsmatrizen , Achse-Winkel und Eulerwinkel Darstellung in:
1 notwendiger Speicherbedarf

## Vergleich der Ezienz

Vergleich von Quaternionen, Rotationsmatrizen , Achse-Winkel und Eulerwinkel Darstellung in:
1 | notwendiger Speicherbedarf
2 | Anzahl Rechenoperationen bei Rotation eines Vektors im R

3

## Vergleich der Ezienz

Vergleich von Quaternionen, Rotationsmatrizen , Achse-Winkel und Eulerwinkel Darstellung in:
1 | notwendiger Speicherbedarf
2 | Anzahl Rechenoperationen bei Rotation eines Vektors im R
| 3
3 | Anzahl Rechenoperationen bei Verkettung zweier Rotationen im R
| 3

## Vergleich der Ezienz-Speicherbedarf

| Quaternion | Matrix | Achse-Winkel | Eulerwinkel
Anzahl Speicherbedarf | 4 | 9 | 3 | 3

## Vergleich der Ezienz-Rotation

| Quaternion | Matrix | Achse-Winkel | Eulerwinkel
Anzahl Additionen | 12 | 6 | 16 | -
Anzahl Multiplikationen | 18 | 9 | 23 | -

## Vergleich der Ezienz-Sequenzen

| Quaternion | Matrix | Achse-Winkel | Eulerwinkel
Anzahl Additionen | 12 | 18 | - | -
Anzahl Multiplikationen | 16 | 27 | - | -

Danke an alle die es bis jetzt ausgehalten haben zuzuhören !
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
