luialvar/ultra_wideband_tumbler/SKITH_old_PCB/Schaltplan_Skith_STM_2.pdf

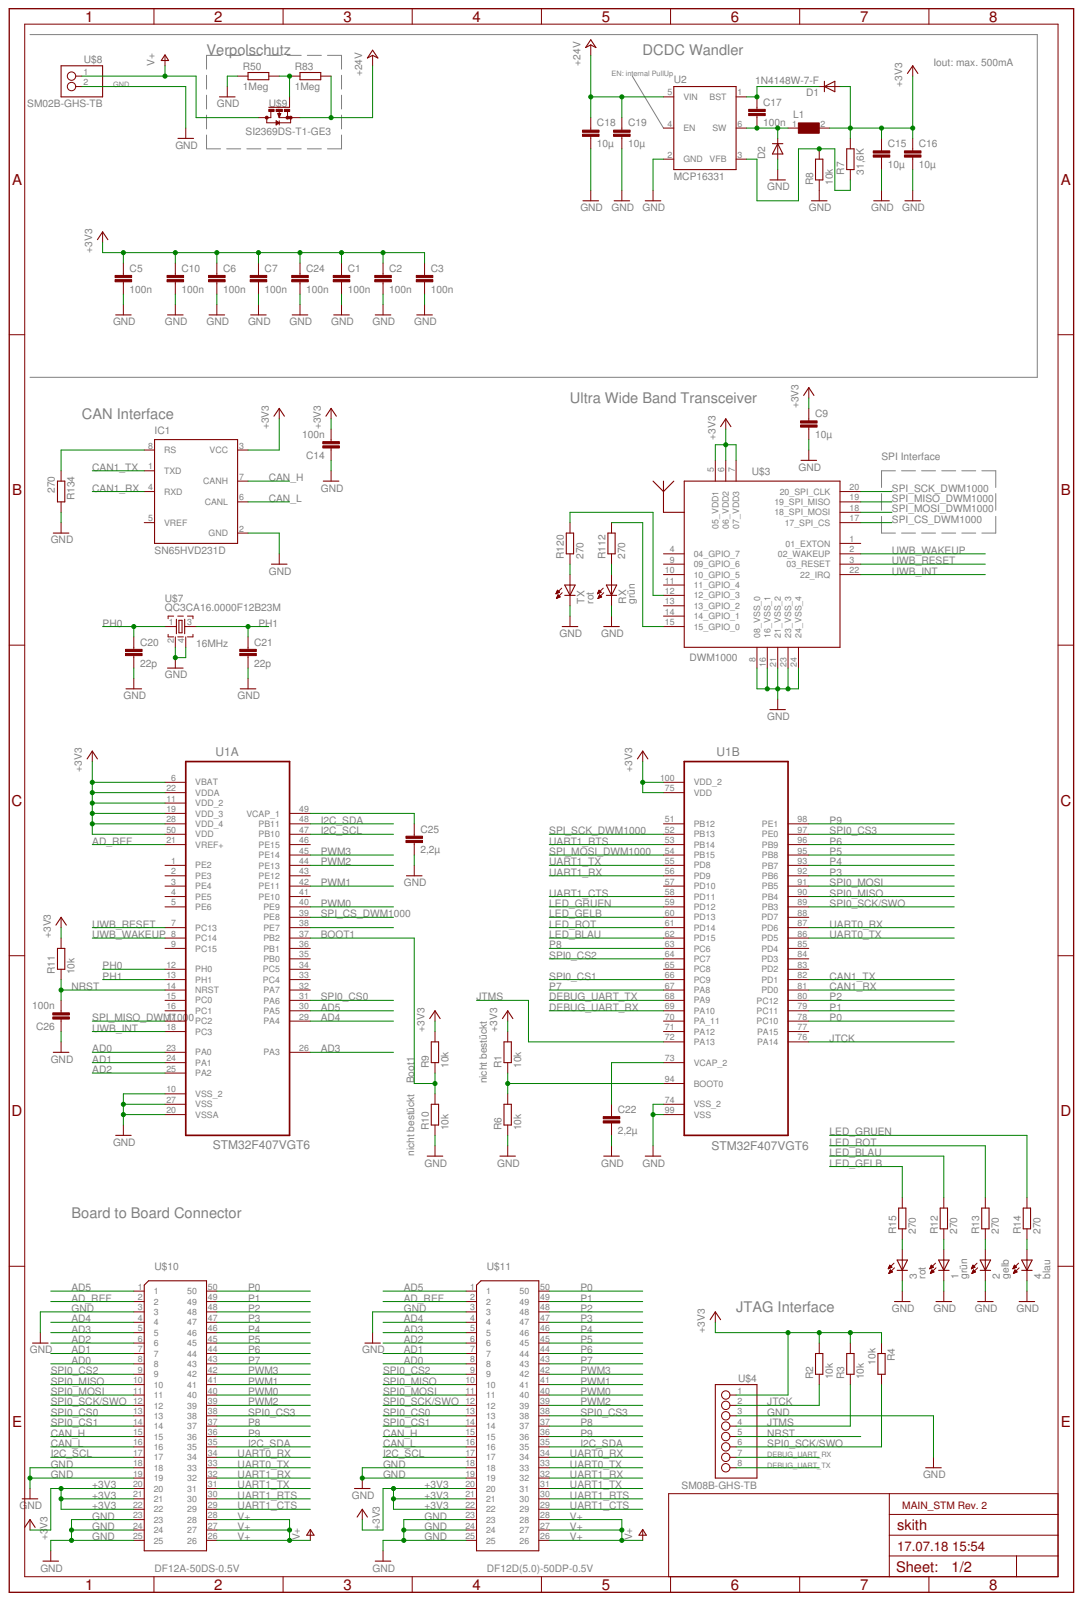
[picture p57: page 1]

EN: internal PullUp Verpolschutz

SPI Interface Ultra Wide Band Transceiver CAN Interface

Board to Board Connector

19 | | 32 UART1_RX | 19 | 32 UART1_RX
20 | | 31 UART1_TX | 20 | 31 UART1_TX SM08B-GHS-TB
21 | | 30 UART1_RTS | 21 | 30 UART1_RTS | MAIN_STM Rev. 2 skith
22 | | 29 UART1_CTS | 22 | 29 UART1_CTS

GND GND GND GND GND
